immortal-sniper1/RP2040_basic_board/LTSpice_simulations/power.asc

C1: cap; 22µ
D1: schottky; 1N5817
M1: pmos; AO4630_P
M2: pmos; AO4630_P
R1: res; 10k
R2: res; 10k
R3: res; 100
R4: res; 0.01
R5: res; 0.01
R6: res; 0.01
V1: voltage; 4
V2: voltage; 4
V3: voltage; 0
Named nets: 0
.tran 15
