immortal-sniper1/RP2040_basic_board/SW/SD_Data_Logger_Make_Delete_File/SD_Data_Logger_Make_Delete_File.ino

/*
  SD card basic file example

  This example shows how to create and destroy an SD card file
  The circuit:
   SD card attached to SPI bus as follows:
 ** MOSI - pin 11
 ** MISO - pin 12
 ** CLK - pin 13
 ** CS - pin 4 (for MKRZero SD: SDCARD_SS_PIN)

  created   Nov 2010
  by David A. Mellis
  modified 9 Apr 2012
  by Tom Igoe

  This example code is in the public domain.

*/

#define SPI_SS_PIN 21
#define SPI_MISO_PIN 20
#define SPI_MOSI_PIN 19
#define SPI_SCK_PIN 18
#define SDcard_detect 22

#include <SPI.h>
#include <SD.h>

File myFile;




/*
#define SPI_SC 5
#define SPI_MISO 4
#define SPI_MOSI 3
#define SPI_SCK 2
#define SDcard_detect 22
*/
int8_t SD_state = 0;


void setup() {
  // Open serial communications and wait for port to open:
  Serial.begin(9600);
  while (!Serial)
  {
    ; // wait for serial port to connect. Needed for native USB port only
  }

  Serial.println("trwsterwe");
  SD_state = digitalRead(SDcard_detect);
  Serial.print("SD card state=");
  Serial.println(SD_state);

  Serial.print("Initializing SD card...");

  if (!SD.begin(4))
  {
    Serial.println("initialization failed!");
    while (1);
  }
  Serial.println("initialization done.");

  if (SD.exists("example.txt"))
  {
    Serial.println("example.txt exists.");
  }
  else
  {
    Serial.println("example.txt doesn't exist.");
  }

  // open a new file and immediately close it:
  Serial.println("Creating example.txt...");
  myFile = SD.open("example.txt", FILE_WRITE);
  myFile.close();

  // Check to see if the file exists:
  if (SD.exists("example2.txt"))
  {
    Serial.println("example2.txt exists.");
  }
  else
  {
    Serial.println("example2.txt doesn't exist.");
  }

  // delete the file:
  Serial.println("Removing example.txt...");
  SD.remove("example2.txt");

  if (SD.exists("example.txt"))
  {
    Serial.println("example.txt exists.");
  }
  else
  {
    Serial.println("example.txt doesn't exist.");
  }
}

void loop()
{
  // nothing happens after setup finishes.
}
